lukasznowarkiewicz/M2SmartHome/images/thermal_image_heatsink.jpg

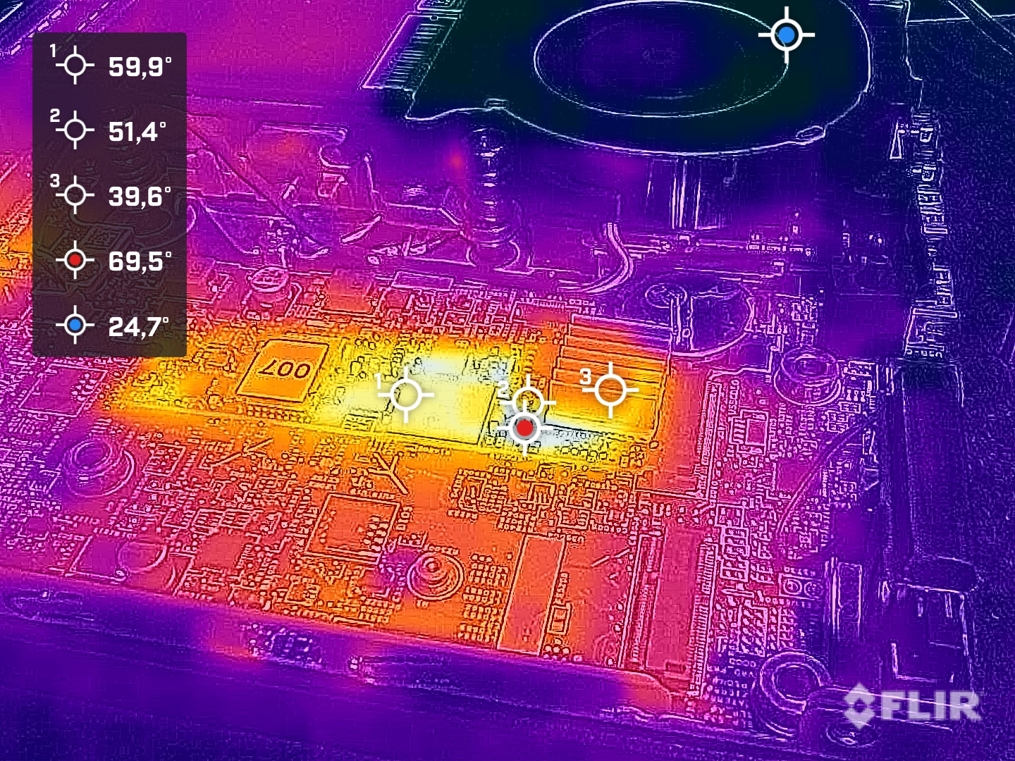
images/thermal_image_heatsink.jpg
