lukasznowarkiewicz/M2SmartHome/hardware-electronics/Spice simulations/i2c_eeprom_ICP/i2c_eeprom_ICP-PSpiceFiles/SCHEMATIC1/simulation/simulation.cir

** Profile: "SCHEMATIC1-simulation"  [ \\Mac\Home\repo\M2SmartHome\hardware-electronics\Spice simulations\i2c_eeprom_ICP\i2c_eeprom_ICP-PSpiceFiles\SCHEMATIC1\simulation.sim ] 

** Creating circuit file "simulation.cir" 
** WARNING: THIS AUTOMATICALLY GENERATED FILE MAY BE OVERWRITTEN BY SUBSEQUENT SIMULATIONS

*Libraries: 
* Profile Libraries :
* Local Libraries :
* From [PSPICE NETLIST] section of C:\cds_spb_home\cdssetup\OrCAD_PSpiceTIPSpice_Install\23.1.0\PSpice.ini file:
.lib "nom_pspti.lib" 
.lib "nom.lib" 

*Analysis directives: 
.TRAN  0 100u 0 
.OPTIONS ADVCONV
.OPTIONS FILEMODELSEARCH
.PROBE64 V(alias(*)) I(alias(*)) W(alias(*)) D(alias(*)) NOISE(alias(*)) 
.INC "..\SCHEMATIC1.net" 


.END
